Daniyar1239/Bionic-prosthesis-on-Arduino/Prosthetic Arm 3D files/Thumb Middle.SLDPRT

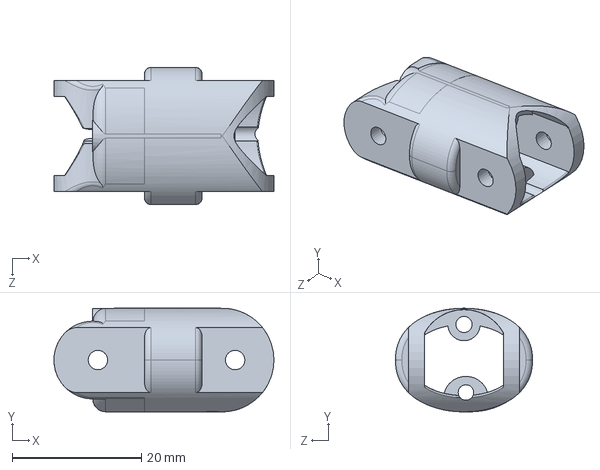
[picture p27: CAD file, 2022-12-16]
Prosthetic Arm 3D files/Thumb Middle.SLDPRT
34.0 x 16.0 x 21.2 mm
