Daniyar1239/Bionic-prosthesis-on-Arduino/Prosthetic Arm 3D files/Palm _ Optimised Connector.SLDPRT

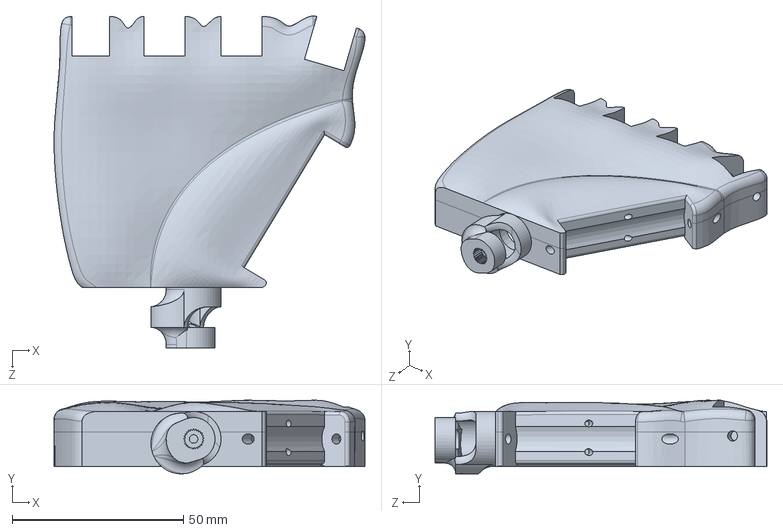
[picture p28: CAD file, 2022-12-16]
Prosthetic Arm 3D files/Palm _ Optimised Connector.SLDPRT
90.8 x 21.5 x 96.9 mm
