Daniyar1239/Bionic-prosthesis-on-Arduino/Prosthetic Arm 3D files/spur gear_iso.sldprt

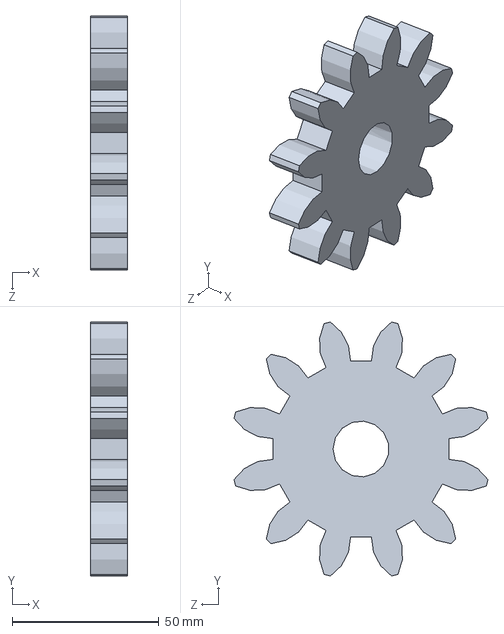
[picture p29: CAD file, 2022-12-16]
Prosthetic Arm 3D files/spur gear_iso.sldprt
12.7 x 86.4 x 86.4 mm
