Daniyar1239/Bionic-prosthesis-on-Arduino/Prosthetic Arm 3D files/Thumb tip 2.SLDPRT

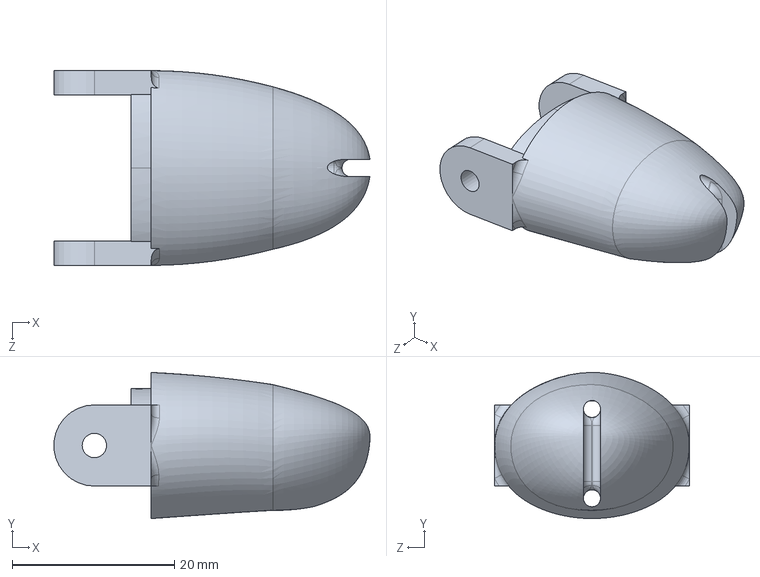
[picture p30: CAD file, 2022-12-16]
Prosthetic Arm 3D files/Thumb tip 2.SLDPRT
38.9 x 18.0 x 24.0 mm
