Daniyar1239/Bionic-prosthesis-on-Arduino/Prosthetic Arm 3D files/Forearm.SLDPRT

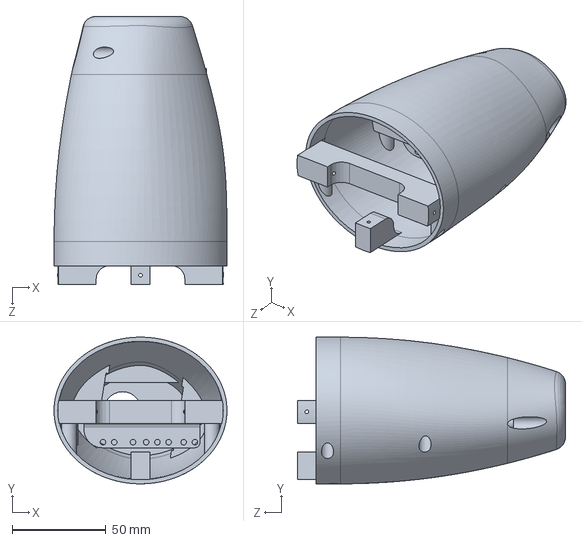
[picture p31: CAD file, 2022-12-16]
Prosthetic Arm 3D files/Forearm.SLDPRT
92.2 x 78.2 x 142.9 mm
